Vacant0mens/boost58_kb/ergogen/output/pcbs/Steps and STLs/WedgeBottom.dxf

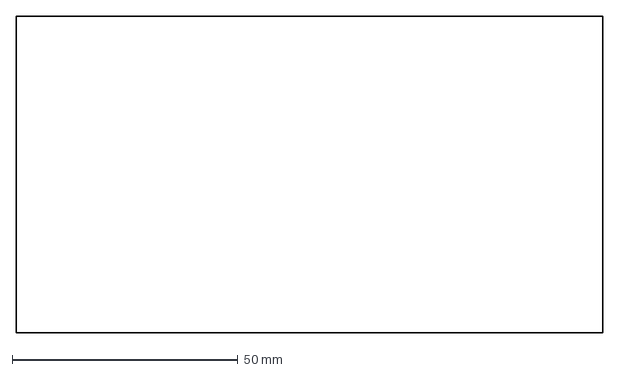
[picture p17: CAD file, 2024-09-02]
ergogen/output/pcbs/Steps and STLs/WedgeBottom.dxf
129.9 x 70.0 mm
