Vacant0mens/boost58_kb/ergogen/output/pcbs/Steps and STLs/BottomCase v3.stl

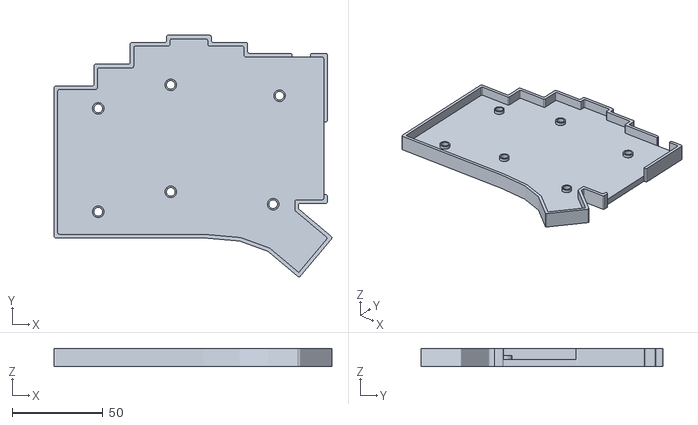
[picture p18: CAD file, 2024-09-02]
ergogen/output/pcbs/Steps and STLs/BottomCase v3.stl
153.3 x 133.3 x 10.0
