Vacant0mens/boost58_kb/ergogen/output/pcbs/Steps and STLs/TopPlate v2.stl

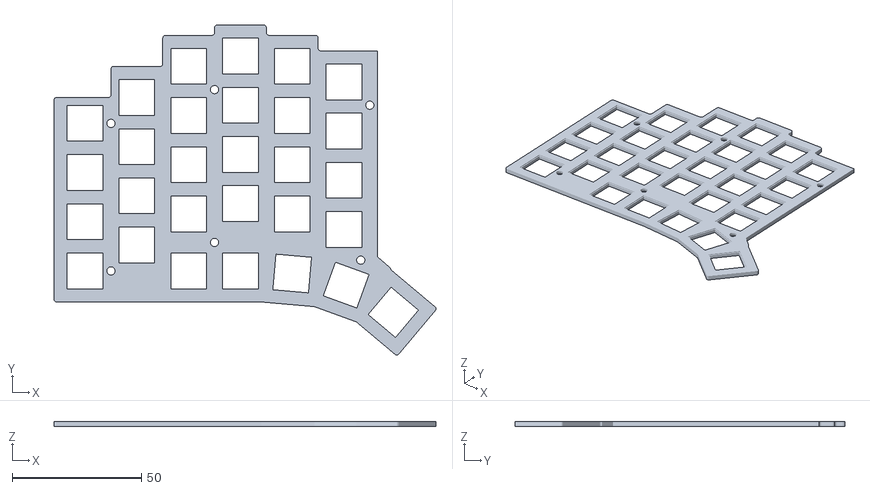
[picture p19: CAD file, 2024-08-24]
ergogen/output/pcbs/Steps and STLs/TopPlate v2.stl
147.5 x 127.5 x 2.00
