Vacant0mens/boost58_kb/ergogen/output/pcbs/Steps and STLs/bottom_case v4.stl

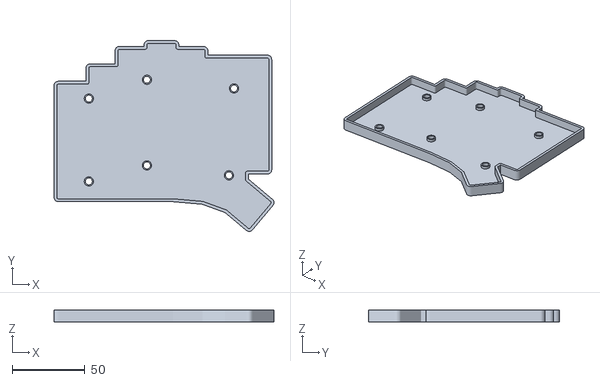
[picture p20: CAD file, 2024-08-20]
ergogen/output/pcbs/Steps and STLs/bottom_case v4.stl
151.5 x 131.5 x 8.00
